fzantalis/night-sky-radar/src/TleFetcher.cpp

#include "TleFetcher.h"
#include "TleStore.h"

#include <HTTPClient.h>
#include <WiFiClientSecure.h>
#include <cstring>

namespace {

// Deviation from the task-9 brief's Step 2/3, recorded here for the record:
//
// Neither `x509_crt_imported_bundle_bin_start` nor `x509_crt_bundle_start`
// exists in this toolchain (framework-arduinoespressif32 3.20007.0, i.e.
// arduino-esp32 2.0.7, via platform espressif32 6.1.0). Both are undefined
// references at COMPILE time, not link time - grepping the whole framework
// and platform package trees for any generated cert-bundle object or the
// python step that produces one turns up nothing. `WiFiClientSecure`'s
// `setCACertBundle()` exists, but arduino-esp32's PlatformIO packaging never
// runs the ESP-IDF/menuconfig CMake step that embeds a default trust bundle
// and emits those symbols, so there is no default bundle to point at on this
// toolchain - not a naming difference, an actually-absent artifact.
//
// The project's global TLS constraint forbids both setInsecure() AND pinning
// a single root (a single pin bricks fetching the day the CA rotates - the
// exact failure mode CelesTrak's own history of switching CAs makes plausible
// for a device meant to run unattended for years). So this is a small,
// concatenated multi-root trust store, not a bundle and not a single pin.
// `WiFiClientSecure::setCACert()` calls `mbedtls_x509_crt_parse()`, which
// accepts multiple concatenated PEM certificates and adds every one of them
// to the trust store - confirmed against ssl_client.cpp in this framework.
// Five self-signed roots below cover the overwhelming majority of what a
// site like CelesTrak would plausibly rotate to: Sectigo's current root
// (the one actually signing celestrak.org today), Sectigo's long-standing
// legacy root, Let's Encrypt (the single most likely fallback for a small
// public site), and the two most common commercial/hosting roots. Each was
// pulled from curl.se's Mozilla-derived CA bundle (the canonical multi-CA
// distribution point, not typed from memory) and independently verified
// self-signed/unexpired with `openssl x509 -noout -subject -issuer -dates`
// before being embedded; see task-9-report.md for the fingerprints and the
// `openssl verify` / `crl2pkcs7` sanity checks run against this exact blob.
constexpr char kTrustedRootsPem[] = R"PEM(-----BEGIN CERTIFICATE-----
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
-----END CERTIFICATE-----
-----BEGIN CERTIFICATE-----
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
Q+6IHdfGjjxDah2nGN59PRbxYvnKkKj9
-----END CERTIFICATE-----
-----BEGIN CERTIFICATE-----
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
m+kXQ99b21/+jh5Xos1AnX5iItreGCc=
-----END CERTIFICATE-----
-----BEGIN CERTIFICATE-----
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
MrY=
-----END CERTIFICATE-----
-----BEGIN CERTIFICATE-----
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
-----END CERTIFICATE-----
)PEM";

}  // namespace

namespace tlefetcher {

const char* trustedRootsPem() { return kTrustedRootsPem; }

bool fetchGroup(const char* group, String& outRaw) {
    outRaw = String();

    String url = "https://celestrak.org/NORAD/elements/gp.php?GROUP=";
    url += group;
    url += "&FORMAT=tle";

    bool ok = false;

    // Scoped so the TLS client and its ~40-50 KB of internal heap are released
    // the moment we are done, before anything else allocates.
    {
        WiFiClientSecure client;
        client.setCACert(kTrustedRootsPem);
        client.setTimeout(15000);

        HTTPClient http;
        http.setConnectTimeout(15000);
        http.setTimeout(15000);
        http.setUserAgent("esp32-sky-radar/0.1");

        if (!http.begin(client, url)) {
            Serial.println("[tle] http begin failed");
            return false;
        }

        const int code = http.GET();
        if (code == HTTP_CODE_OK) {
            outRaw = http.getString();
            ok = outRaw.length() > 0;
        } else {
            Serial.printf("[tle] GET failed, code %d\n", code);
        }

        http.end();
    }

    if (!ok) return false;

    Serial.printf("[tle] fetched %u bytes for group %s\n",
                  static_cast<unsigned>(outRaw.length()), group);
    return true;
}

// Streams a CelesTrak group without ever holding the whole body. See the
// declaration in TleFetcher.h for the full contract.
int fetchGroupStreaming(const char* group, TleFilter keep, std::vector<Tle>& out,
                        int maxKeep, int* totalParsed, uint32_t* minFreeHeapOut) {
    out.clear();
    if (totalParsed) *totalParsed = 0;

    uint32_t minFreeHeap = ESP.getFreeHeap();
    auto trackHeap = [&]() {
        const uint32_t free = ESP.getFreeHeap();
        if (free < minFreeHeap) minFreeHeap = free;
    };

    String url = "https://celestrak.org/NORAD/elements/gp.php?GROUP=";
    url += group;
    url += "&FORMAT=tle";

    int accepted = 0;
    int seenTriples = 0;

    {
        WiFiClientSecure client;
        client.setCACert(kTrustedRootsPem);
        client.setTimeout(15000);

        HTTPClient http;
        http.setConnectTimeout(15000);
        http.setTimeout(15000);
        http.setUserAgent("esp32-sky-radar/0.1");

        if (!http.begin(client, url)) {
            Serial.println("[tle] streaming http begin failed");
            return -1;
        }

        const int code = http.GET();
        if (code != HTTP_CODE_OK) {
            Serial.printf("[tle] streaming GET failed, code %d\n", code);
            http.end();
            return -1;
        }

        trackHeap();

        WiFiClient* stream = http.getStreamPtr();
        const long contentLen = http.getSize();   // -1 if unknown/chunked

        // Bounded per-line buffer: a TLE line is 69 columns, a name at most
        // 24. 160 bytes is generous headroom without ever approaching the
        // ~1.7 MB the whole body would take. Nothing larger than one line is
        // ever resident, and nothing larger than one three-line element set
        // (triple[3]) is ever held across iterations.
        constexpr size_t kLineBufSize = 160;
        char lineBuf[kLineBufSize];
        char triple[3][kLineBufSize];
        int held = 0;
        long totalRead = 0;

        for (;;) {
            if (contentLen >= 0 && totalRead >= contentLen) break;   // consumed the declared body
            if (!http.connected() && !stream->available()) break;    // socket closed, nothing buffered

            const int n = static_cast<int>(stream->readBytesUntil('\n', lineBuf, kLineBufSize - 1));
            if (n <= 0) {
                if (!http.connected()) break;   // genuinely done, not just a brief stall
                continue;
            }
            totalRead += static_cast<long>(n) + 1;
            lineBuf[n] = '\0';

            // Trim a trailing '\r' and any padding, same as parseTleText().
            int end = n;
            while (end > 0 && (lineBuf[end - 1] == '\r' || lineBuf[end - 1] == ' ')) end--;
            lineBuf[end] = '\0';
            int start = 0;
            while (lineBuf[start] == ' ') start++;
            if (start >= end) { trackHeap(); continue; }   // blank line between triples

            std::strncpy(triple[held], lineBuf + start, kLineBufSize - 1);
            triple[held][kLineBufSize - 1] = '\0';
            held++;
            if (held < 3) { trackHeap(); continue; }

            held = 0;
            Tle t;
            if (parseTle(triple[0], triple[1], triple[2], t)) {
                seenTriples++;
                if (keep(t) && static_cast<int>(out.size()) < maxKeep) {
                    out.push_back(t);
                    accepted++;
                }
            } else {
                Serial.printf("[tle] streaming skipped malformed entry: %s\n", triple[0]);
            }
            trackHeap();
        }

        http.end();
    }

    if (totalParsed) *totalParsed = seenTriples;
    if (minFreeHeapOut) *minFreeHeapOut = minFreeHeap;

    Serial.printf("[tle] streaming fetch of '%s': %d triple(s) parsed, %d kept, "
                  "min free heap %u bytes\n",
                  group, seenTriples, accepted, static_cast<unsigned>(minFreeHeap));

    return accepted;
}

}  // namespace tlefetcher

int parseTleText(const String& raw, std::vector<Tle>& out, int maxCount) {
    out.clear();

    const int n = static_cast<int>(raw.length());
    String triple[3];
    int held = 0;
    int i = 0;

    // Walk the buffer one line at a time, holding at most three lines. This
    // does NOT make the whole body cheap - `raw` is already fully resident by
    // the time this runs, since fetchGroup() (the only caller for `stations`/
    // `visual`) reads the whole response into one Arduino String first. That
    // is fine for those two groups (~4 KB / ~22 KB) but is exactly why the
    // ~1.7 MB `starlink` group needs fetchGroupStreaming() instead, which
    // never materialises the body at all. A previous comment here claimed
    // this function was what made Starlink tractable; it was not - a
    // reviewer flagged it during M0-M1, and it is corrected here at M3.
    while (i < n && static_cast<int>(out.size()) < maxCount) {
        int nl = raw.indexOf('\n', i);
        if (nl < 0) nl = n;

        String line = raw.substring(i, nl);
        i = nl + 1;

        line.replace("\r", "");
        line.trim();
        if (line.length() == 0) continue;

        triple[held++] = line;
        if (held < 3) continue;

        held = 0;
        Tle t;
        if (parseTle(triple[0].c_str(), triple[1].c_str(), triple[2].c_str(), t)) {
            out.push_back(t);
        } else {
            Serial.printf("[tle] skipped malformed entry: %s\n", triple[0].c_str());
        }
    }

    return static_cast<int>(out.size());
}
